ShawnHymel/crommeter/hardware/artwork/cromulon.png

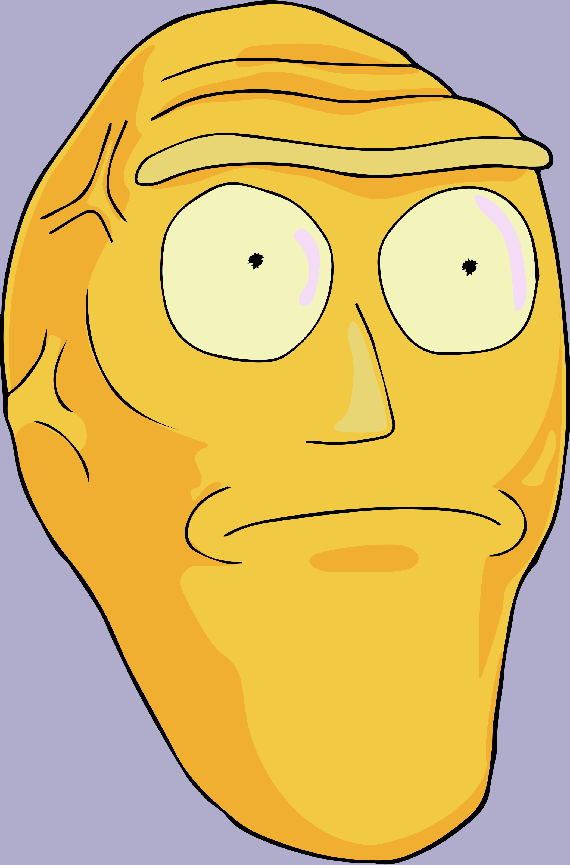
hardware/artwork/cromulon.png
