ShawnHymel/crommeter/references/rp235x-stamp-schematic.png

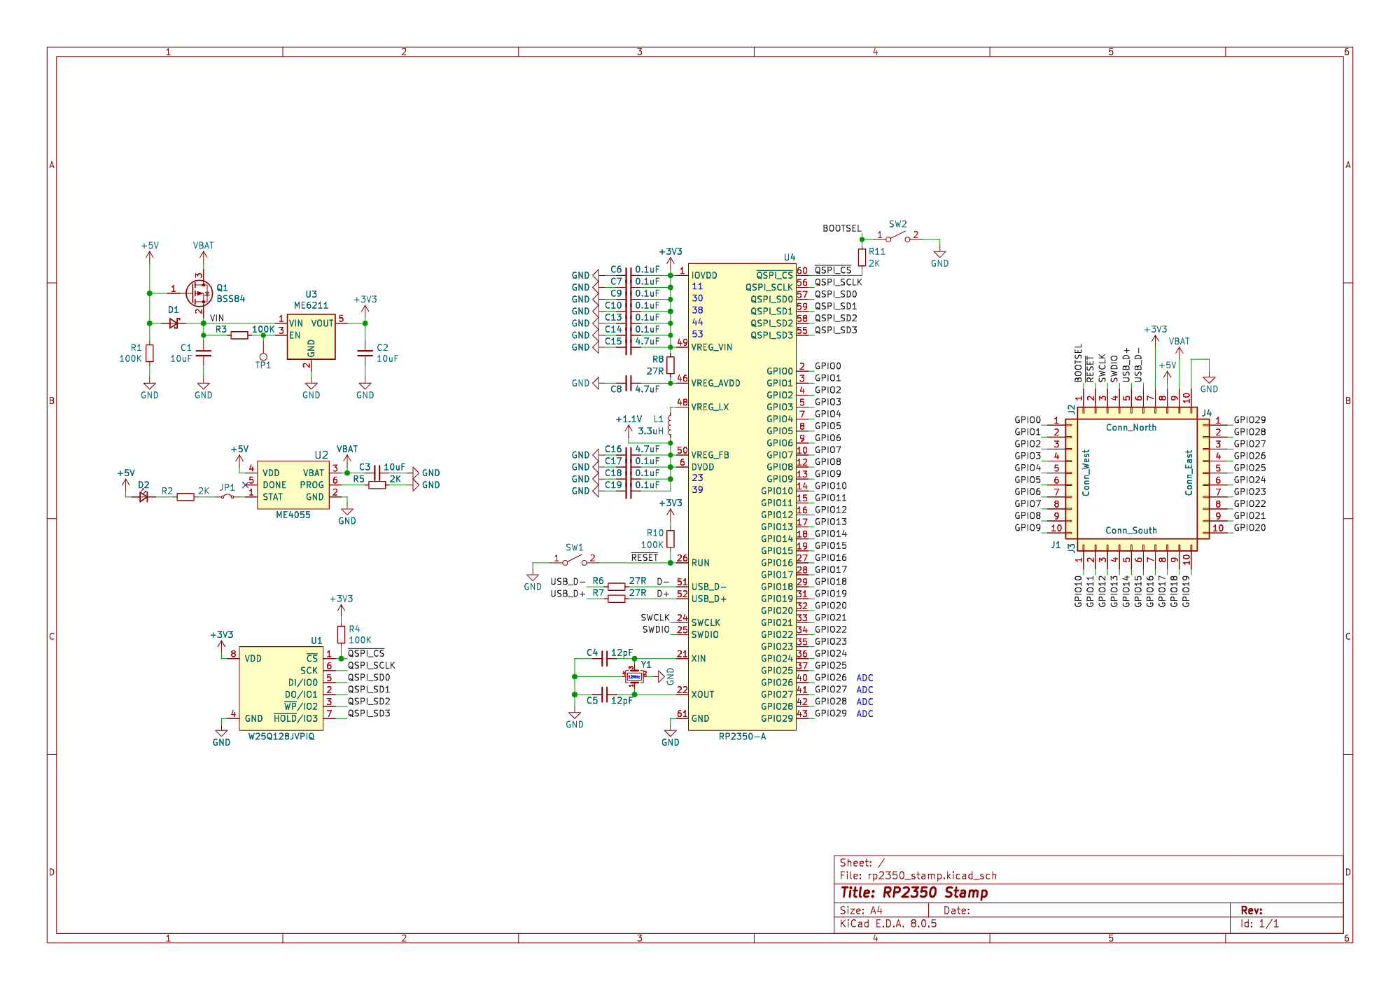
references/rp235x-stamp-schematic.png
