ShawnHymel/crommeter/firmware/arduino/test_leds/test_leds.ino

// the setup function runs once when you press reset or power the board
void setup() {
  // Eyes
  pinMode(16, OUTPUT);
  pinMode(17, OUTPUT);

  // 7 Segment display
  pinMode(10, OUTPUT);
  pinMode(11, OUTPUT);
  pinMode(12, OUTPUT);

  digitalWrite(10, HIGH);
  digitalWrite(11, HIGH);
  digitalWrite(12, HIGH);

  pinMode(2, OUTPUT);
  pinMode(3, OUTPUT);
  pinMode(4, OUTPUT);
  pinMode(5, OUTPUT);
  pinMode(6, OUTPUT);
  pinMode(7, OUTPUT);
  pinMode(8, OUTPUT);
  pinMode(9, OUTPUT);
}

// the loop function runs over and over again forever
void loop() {
  digitalWrite(16, HIGH);  // turn the LED on (HIGH is the voltage level)
  digitalWrite(17, HIGH); 
  digitalWrite(12, HIGH);
  digitalWrite(2, LOW);
  digitalWrite(3, LOW);
  digitalWrite(4, LOW);
  digitalWrite(5, LOW);
  digitalWrite(6, LOW);
  digitalWrite(7, LOW);
  digitalWrite(8, LOW);
  digitalWrite(9, LOW);
  delay(1000);                      // wait for a second
  digitalWrite(16, LOW);   // turn the LED off by making the voltage LOW
  digitalWrite(17, LOW); 
  digitalWrite(2, HIGH);
  digitalWrite(3, HIGH);
  digitalWrite(4, HIGH);
  digitalWrite(5, HIGH);
  digitalWrite(6, HIGH);
  digitalWrite(7, HIGH);
  digitalWrite(8, HIGH);
  digitalWrite(9, HIGH);
  delay(1000);                      // wait for a second
}
